uhppoted/uhppoted-wiegand/breadboard/pico/core/src/relays.c

#include <stdio.h>

#include "hardware/rtc.h"

#include "../include/TPIC6B595.h"
#include "../include/logd.h"
#include "../include/relays.h"

enum RELAY_STATE {
    TRANSITION = 1,
    NORMALLY_OPEN = 2,
    NORMALLY_CLOSED = 3,
    RELAY_ERROR = 4,
    FAILED = 5
};

enum DOOR_CONTACT_STATE {
    DOOR_OPEN = 1,
    DOOR_CLOSED = 2
};

enum PUSHBUTTON_STATE {
    RELEASED = 1,
    PRESSED = 2
};

bool relay_monitor(repeating_timer_t *);
int64_t relay_timeout(alarm_id_t, void *);

/* Initialises the monitor for relay normally open ('NO') and normally
 * closed ('NC') inputs.
 *
 */
bool relay_initialise(enum MODE mode) {
    static repeating_timer_t relay_rt;

    if (mode == CONTROLLER) {
        TPIC_set(DOOR_UNLOCK, false);
    }

    return add_repeating_timer_ms(1, relay_monitor, NULL, &relay_rt);
}

float lpf(bool b, float v) {
    return v += b ? 0.01 * (1.0 - v) : 0.01 * (0.0 - v);
}

bool relay_monitor(repeating_timer_t *rt) {
    static enum RELAY_STATE state1 = -1;
    static enum DOOR_CONTACT_STATE state2 = -1;
    static enum PUSHBUTTON_STATE state3 = -1;

    static float vfailed = 0.5;
    static float vunknown = 0.5;
    static float verror = 0.5;
    static float vopen = 0.5;
    static float vclosed = 0.5;
    static bool normally_open = false;
    static bool normally_closed = false;
    static float vdoor = 0.5;
    static float vbutton = 0.5;

    enum RELAY_STATE current1 = 0xff;
    enum DOOR_CONTACT_STATE current2 = 0xff;
    enum PUSHBUTTON_STATE current3 = 0xff;

    bool no = gpio_get(RELAY_NO) == 0;
    bool nc = gpio_get(RELAY_NC) == 0;
    bool door = gpio_get(DOOR_SENSOR) == 0;
    bool button = gpio_get(PUSH_BUTTON) == 0;

    verror = lpf(no && nc, verror);
    vopen = lpf(no && !nc, vopen);
    vclosed = lpf(!no && nc, vclosed);
    vunknown = lpf(!no && !nc, vunknown);
    vfailed = lpf(verror < 0.9 && vopen < 0.9 && vclosed < 0.9 && vunknown < 0.9, vfailed);
    vdoor = lpf(door, vdoor);
    vbutton = lpf(button, vbutton);

    if (verror > 0.9 && vopen < 0.9 && vclosed < 0.9 && vunknown < 0.9) {
        current1 = RELAY_ERROR;
    } else if (verror < 0.9 && vopen > 0.9 && vclosed < 0.9 && vunknown < 0.9) {
        current1 = NORMALLY_OPEN;
    } else if (verror < 0.9 && vopen < 0.9 && vclosed > 0.9 && vunknown < 0.9) {
        current1 = NORMALLY_CLOSED;
    } else if (verror < 0.9 && vopen < 0.9 && vclosed < 0.9 && vunknown > 0.9) {
        current1 = UNKNOWN;
    } else if (vfailed > 0.9) {
        current1 = FAILED;
    }

    if (vdoor > 0.9) {
        current2 = DOOR_CLOSED;
    } else if (vdoor < 0.1) {
        current2 = DOOR_OPEN;
    }

    if (vbutton > 0.9) {
        current3 = PRESSED;
    } else if (vdoor < 0.1) {
        current3 = RELEASED;
    }

    if (current1 != 0xff && current1 != state1) {
        uint32_t msg = MSG_RELAY;

        if (current1 == UNKNOWN) {
            msg |= 0x0000;
        } else if (current1 == NORMALLY_OPEN) {
            msg |= 0x0001;
        } else if (current1 == NORMALLY_CLOSED) {
            msg |= 0x0002;
        } else if (current1 == RELAY_ERROR) {
            msg |= 0x0003;
        } else if (current1 == FAILED) {
            msg |= 0x0004;
        } else {
            msg |= 0xffff;
        }

        if (!queue_is_full(&queue) && queue_try_add(&queue, &msg)) {
            state1 = current1;
        }
    }

    if (current2 != 0xff && current2 != state2) {
        uint32_t msg = MSG_DOOR;

        if (current2 == UNKNOWN) {
            msg |= 0x0000;
        } else if (current2 == DOOR_OPEN) {
            msg |= 0x0001;
        } else if (current2 == DOOR_CLOSED) {
            msg |= 0x0002;
        } else {
            msg |= 0xffff;
        }

        if (!queue_is_full(&queue) && queue_try_add(&queue, &msg)) {
            state2 = current2;
        }
    }

    if (current3 != 0xff && current3 != state3) {
        uint32_t msg = MSG_PUSHBUTTON;

        if (current3 == UNKNOWN) {
            msg |= 0x0000;
        } else if (current3 == PRESSED) {
            msg |= 0x0001;
        } else if (current3 == RELEASED) {
            msg |= 0x0002;
        } else {
            msg |= 0xffff;
        }

        if (!queue_is_full(&queue) && queue_try_add(&queue, &msg)) {
            state3 = current3;
        }
    }

    return true;
}

/* Handler for a RELAY event.
 *
 */
void relay_event(uint32_t v) {
    if (v == 0x0000) {
        logd_log("DOOR   LOCK UNKNOWN");
    } else if (v == 0x0001) {
        logd_log("DOOR   LOCKED");
    } else if (v == 0x0002) {
        logd_log("DOOR   UNLOCKED");
    } else if (v == 0x0003) {
        logd_log("DOOR   LOCK ERROR");
    } else if (v == 0x0004) {
        logd_log("DOOR   LOCK FAILED");
    } else {
        logd_log("DOOR   LOCK ????");
    }
}

/* Sets the DOOR OPEN relay (CONTROLLER mode only).
 *
 */
void door_unlock(uint32_t delay) {
    if (mode == CONTROLLER) {
        if (add_alarm_in_ms(delay, relay_timeout, NULL, false) > 0) {
            TPIC_set(DOOR_UNLOCK, true);
        }
    }
}

/* Sets/clears the DOOR CONTACT emulation relay (EMULATOR mode only).
 *
 */
void relay_door_contact(bool closed) {
    if (mode == EMULATOR) {
        TPIC_set(DOOR_CONTACT, closed);
    }
}

/* Sets/clears the PUSHBUTTON emulation relay (EMULATOR mode only).
 *
 */
void relay_pushbutton(bool closed) {
    if (mode == EMULATOR) {
        TPIC_set(PUSHBUTTON, closed);
    }
}

/* Timeout handler. Clears the DOOR UNLOCK relay.
 *
 */
int64_t relay_timeout(alarm_id_t id, void *data) {
    TPIC_set(DOOR_UNLOCK, false);
    return 0;
}

/* Handler for a DOOR CONTACT input event.
 *
 */
void door_event(uint32_t v) {
    if (v == 0x0000) {
        logd_log("DOOR  UNKNOWN");
    } else if (v == 0x0001) {
        logd_log("DOOR   OPEN");
    } else if (v == 0x0002) {
        logd_log("DOOR   CLOSED");
    } else {
        logd_log("DOOR  ????");
    }
}

/* Handler for a PUSHBUTTON input event.
 *
 */
void pushbutton_event(uint32_t v) {
    if (v == 0x0000) {
        logd_log("BUTTON UNKNOWN");
    } else if (v == 0x0001) {
        logd_log("BUTTON PRESSED");
    } else if (v == 0x0002) {
        logd_log("BUTTON RELEASED");
    } else {
        logd_log("BUTTON ????");
    }
}
