uhppoted/uhppoted-wiegand/breadboard/pico/core/src/uart.c

#include <stdio.h>
#include <stdlib.h>
#include <string.h>

#include "hardware/rtc.h"
#include "pico/util/queue.h"

#include "../include/common.h"

extern void exec(char *cmd);

typedef struct CLI {
    int ix;
    int32_t timer;
    char buffer[64];
} CLI;

const char ESC = 27;
uint8_t height = 25;
const uint32_t CLI_TIMEOUT = 10000;

int64_t cli_timeout(alarm_id_t, void *);
void echo(const char *);
void cpr(char *);
void set_scroll_area();
void clearline();

/** Processes received UART characters.
 *
 */
void rx(char *received) {
    static CLI cli = {
        .ix = 0,
        .timer = -1,
        .buffer = {0},
    };

    if (cli.timer > 0) {
        cancel_alarm(cli.timer);
        cli.timer = 0;
    }

    int N = strlen(received);
    for (int i = 0; i < N; i++) {
        uint8_t ch = received[i];

        // CRLF ?
        if (ch == '\n' || ch == '\r') {
            if (cli.ix > 0) {
                exec(cli.buffer);
            }

            memset(cli.buffer, 0, sizeof(cli.buffer));
            cli.ix = 0;
            continue;
        }

        // VT100 escape code?
        if (cli.buffer[0] == 27 && ch == 'R' && (cli.ix < sizeof(cli.buffer) - 1)) { // VT100 cursor position report
            cli.buffer[cli.ix++] = ch;
            cli.buffer[cli.ix] = 0;

            cpr(&cli.buffer[1]);
            memset(cli.buffer, 0, sizeof(cli.buffer));
            cli.ix = 0;
            continue;
        }

        // backspace?
        if (ch == 8) {
            if (cli.ix > 0) {
                cli.buffer[--cli.ix] = 0;
                echo(cli.buffer);
            }

            if (cli.ix > 0) {
                cli.timer = add_alarm_in_ms(CLI_TIMEOUT, cli_timeout, (CLI *)&cli, true);
            }

            continue;
        }

        // Add character to buffer
        if (cli.ix < sizeof(cli.buffer) - 1) {
            cli.buffer[cli.ix++] = ch;
            cli.buffer[cli.ix] = 0;

            // ... echo if normal commnad and not a VT100 code
            if (cli.buffer[0] != 27) {
                echo(cli.buffer);
            }

            cli.timer = add_alarm_in_ms(CLI_TIMEOUT, cli_timeout, (CLI *)&cli, true);
            continue;
        }
    }
}

/* Timeout handler. Clears the current command and command line.
 *
 */
int64_t cli_timeout(alarm_id_t id, void *data) {
    CLI *cli = (CLI *)data;
    memset(cli->buffer, 0, sizeof(cli->buffer));
    cli->ix = 0;
    cli->timer = 0;

    clearline();

    return 0;
}

/* Saves the cursor position, displays the current command buffer and then restores
 *  the cursor position
 *
 */
void echo(const char *cmd) {
    char s[64];
    snprintf(s, sizeof(s), "\0337\033[%d;0H>> %s\033[0K\0338", height, cmd);
    fputs(s, stdout);
    fflush(stdout);
}

/* Reinitialises the terminal.
 *
 */
void cls() {
    fputs("\033c\033[2J", stdout);
    fflush(stdout);

    set_scroll_area();
}

/* Clears the screen
 *
 */
void clear_screen() {
    fputs("\033[2J", stdout);
    fflush(stdout);
}

/* Requests terminal window size - the scroll area is set from the response.
 *
 */
void set_scroll_area() {
    fputs("\0337\033[999;999H\033[6n\0338", stdout);
    fflush(stdout);
}

/* Saves the cursor position, clears the command line, redisplays the prompt and then
 * restores the cursor position.
 *
 */
void clearline() {
    char s[24];
    snprintf(s, sizeof(s), "\0337\033[%d;0H>> \033[0K\0338", height);
    fputs(s, stdout);
    fflush(stdout);
}

/* Cursor position report.
 *  Sets the scrolling window with space at the bottom for the command echo.
 *
 */
void cpr(char *cmd) {
    int rows;
    int cols;
    int rc = sscanf(cmd, "[%d;%dR", &rows, &cols);

    if (rc > 0) {
        height = rows - 1;

        char s[24];
        snprintf(s, sizeof(s), "\0337\033[0;%dr\0338", height - 2);
        fputs(s, stdout);
        fflush(stdout);

        clearline();
    }
}
