uhppoted/uhppoted-wiegand/breadboard/pico/core/include/logd.h

#pragma once

#include <stdbool.h>

#include "wiegand.h"

extern bool logd_initialise(enum MODE);
extern void logd_terminate();
extern void logd_log(const char *);
extern void logd_debug(const char *);
